jackbrad1ey/thingamaboard_v2/CAD/keycaps/images/MBK_Keycap_-_1u.png

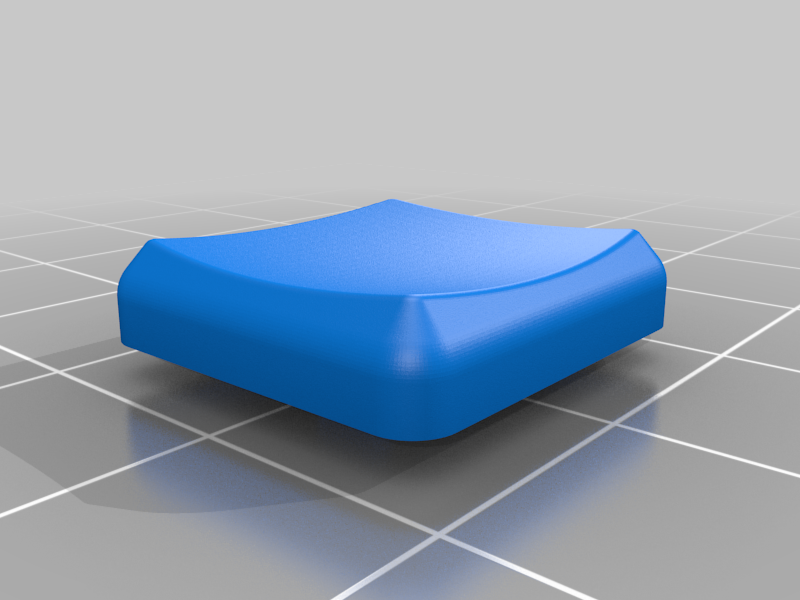
CAD/keycaps/images/MBK_Keycap_-_1u.png
