jackbrad1ey/thingamaboard_v2/CAD/outputs/top_case_drawing.PNG

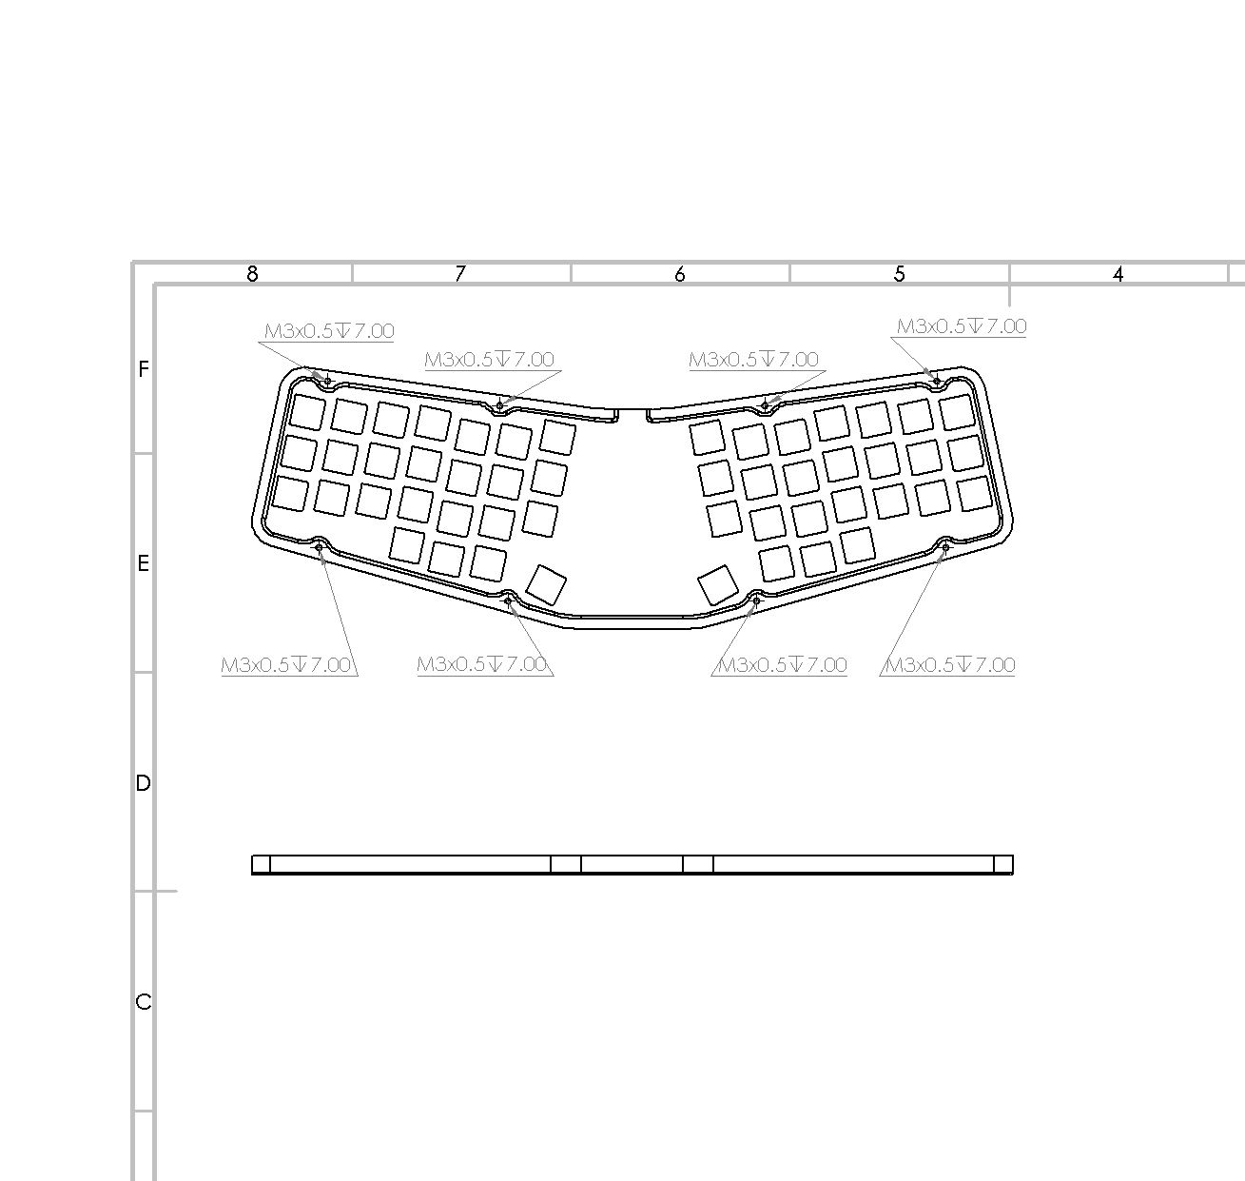
CAD/outputs/top_case_drawing.PNG
