jackbrad1ey/thingamaboard_v2/CAD/1U-keycap.SLDPRT

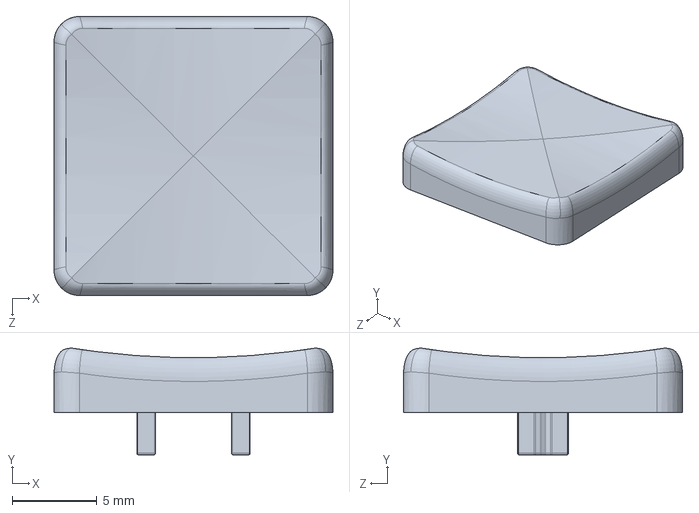
[picture p23: CAD file, 2024-09-15]
CAD/1U-keycap.SLDPRT
16.5 x 6.32 x 16.5 mm
