jackbrad1ey/thingamaboard_v2/CAD/M3_bolt_10mm.SLDPRT

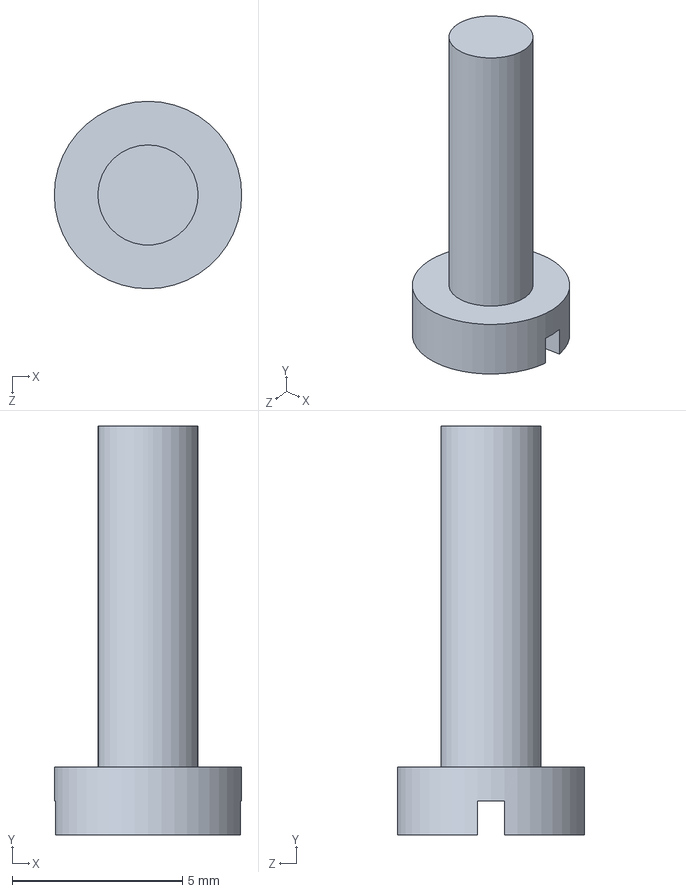
[picture p24: CAD file, 2024-09-24]
CAD/M3_bolt_10mm.SLDPRT
5.50 x 12.0 x 5.50 mm
