jackbrad1ey/thingamaboard_v2/CAD/keyboard.SLDASM

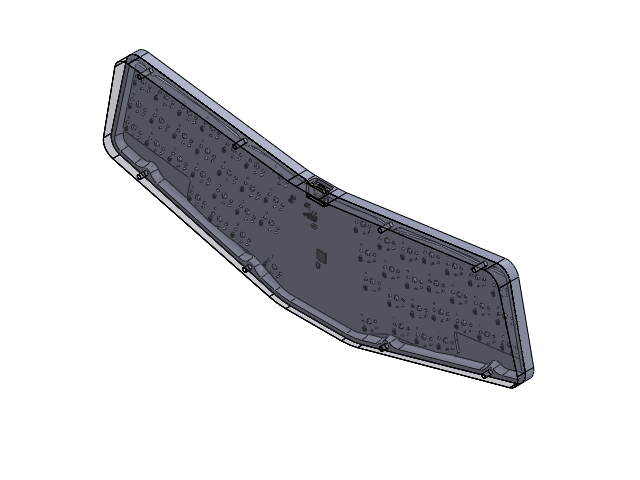
[picture p25: CAD file, 2024-09-14]
CAD/keyboard.SLDASM
top_case_v2
case_bottom
COMPOUND_1.step x 50
SOLID_1.step x 50
SOLID-0_1.step x 13
SOLID-1_1.step x 14
SOLID-2_1.step
SOLID-3.step
SOLID-4.step
SOLID-5.step
SOLID-6.step
SOLID-7.step x 2
SOLID-8.step
SOLID-9.step
SOLID-10.step
SOLID-11.step
SOLID-12.step
keyboard PCB_1.step
