jackbrad1ey/thingamaboard_v2/CAD/outputs/keyboard_assembly.PNG

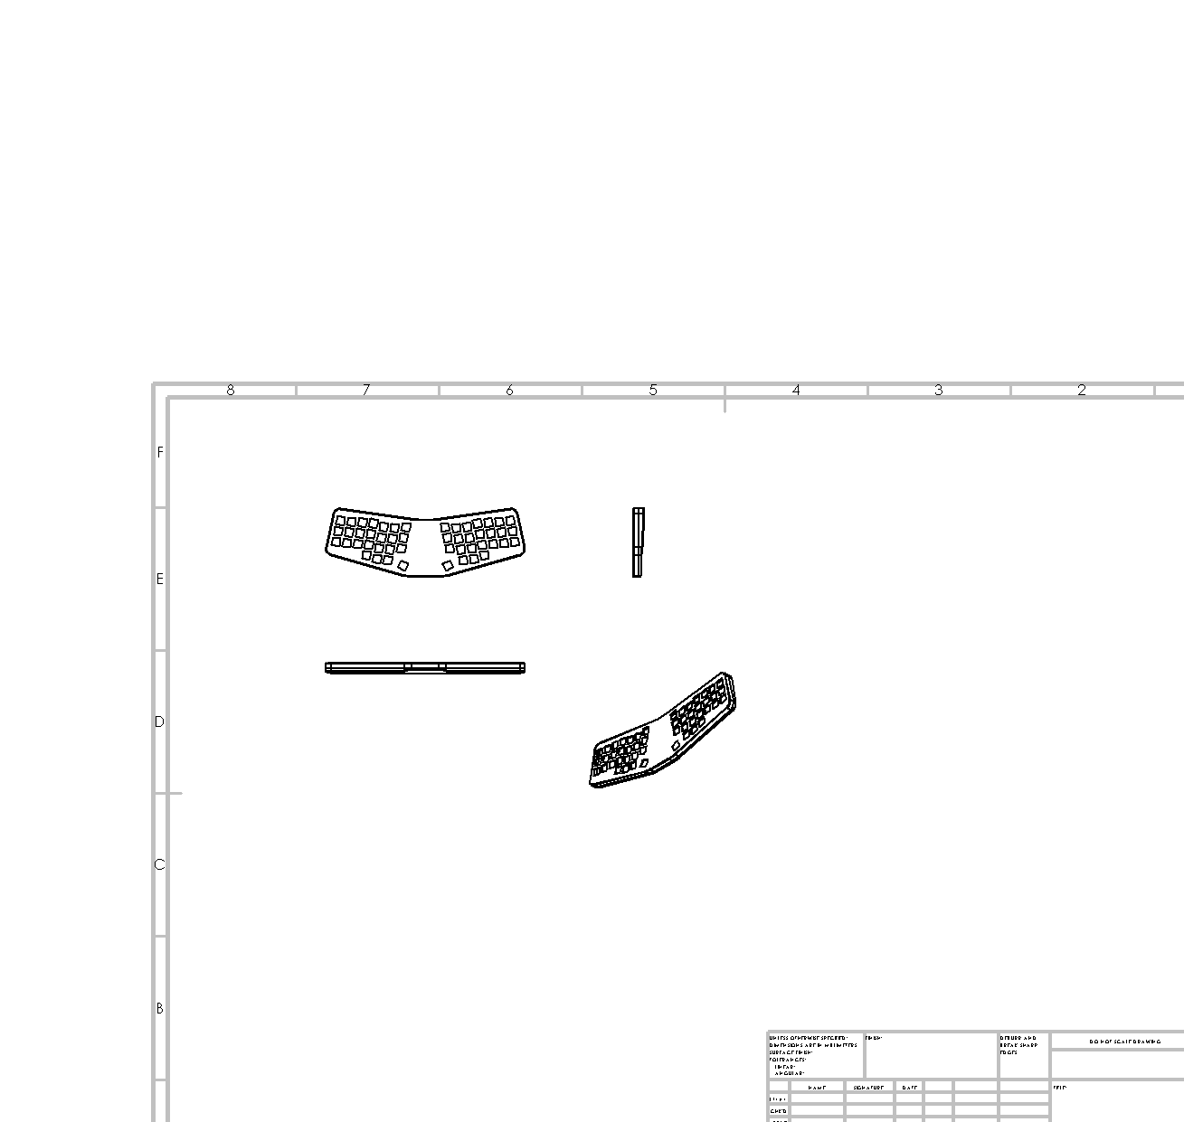
CAD/outputs/keyboard_assembly.PNG
